cchengoran525/HappyMac/training/analysis/02_x_distribution.png

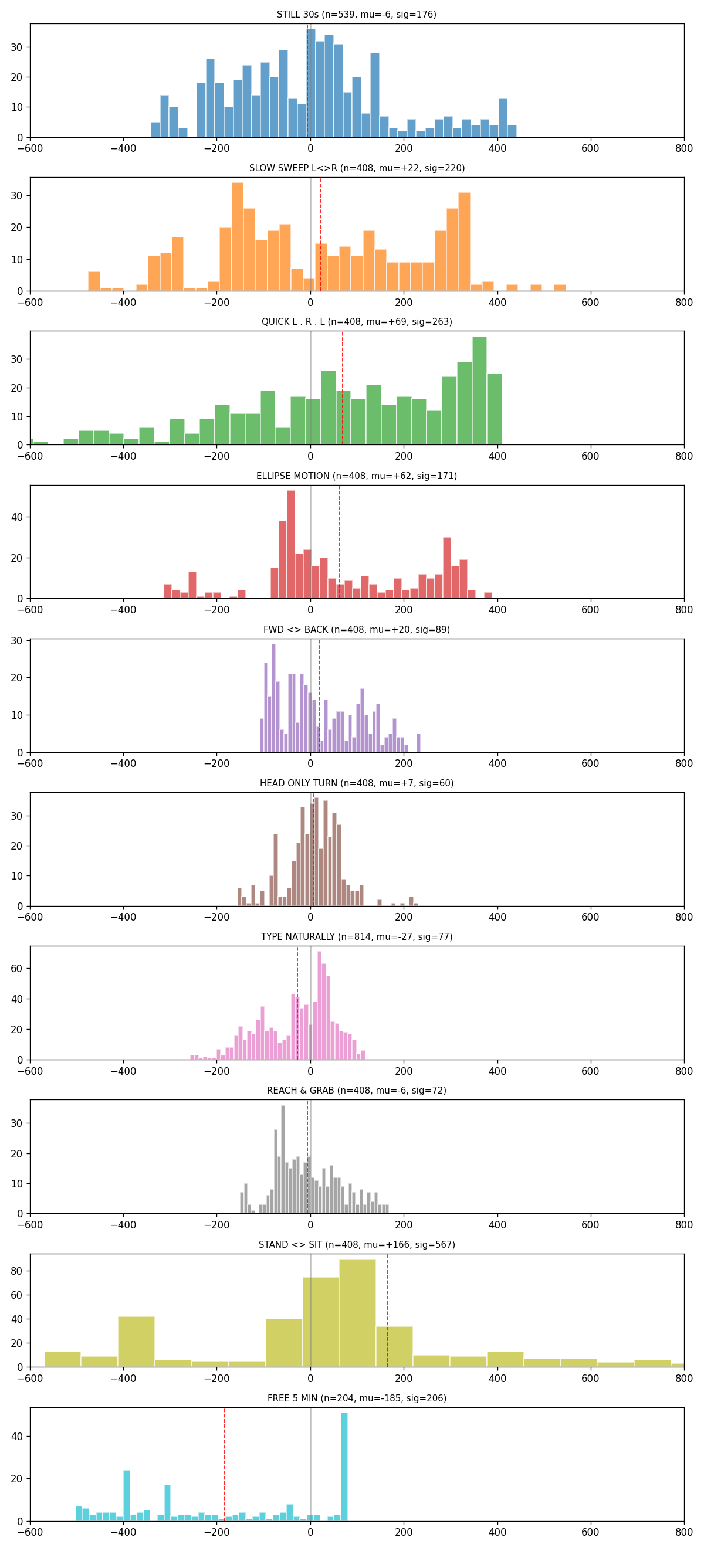
training/analysis/02_x_distribution.png
