cchengoran525/HappyMac/training/analysis/04_drift_analysis.png

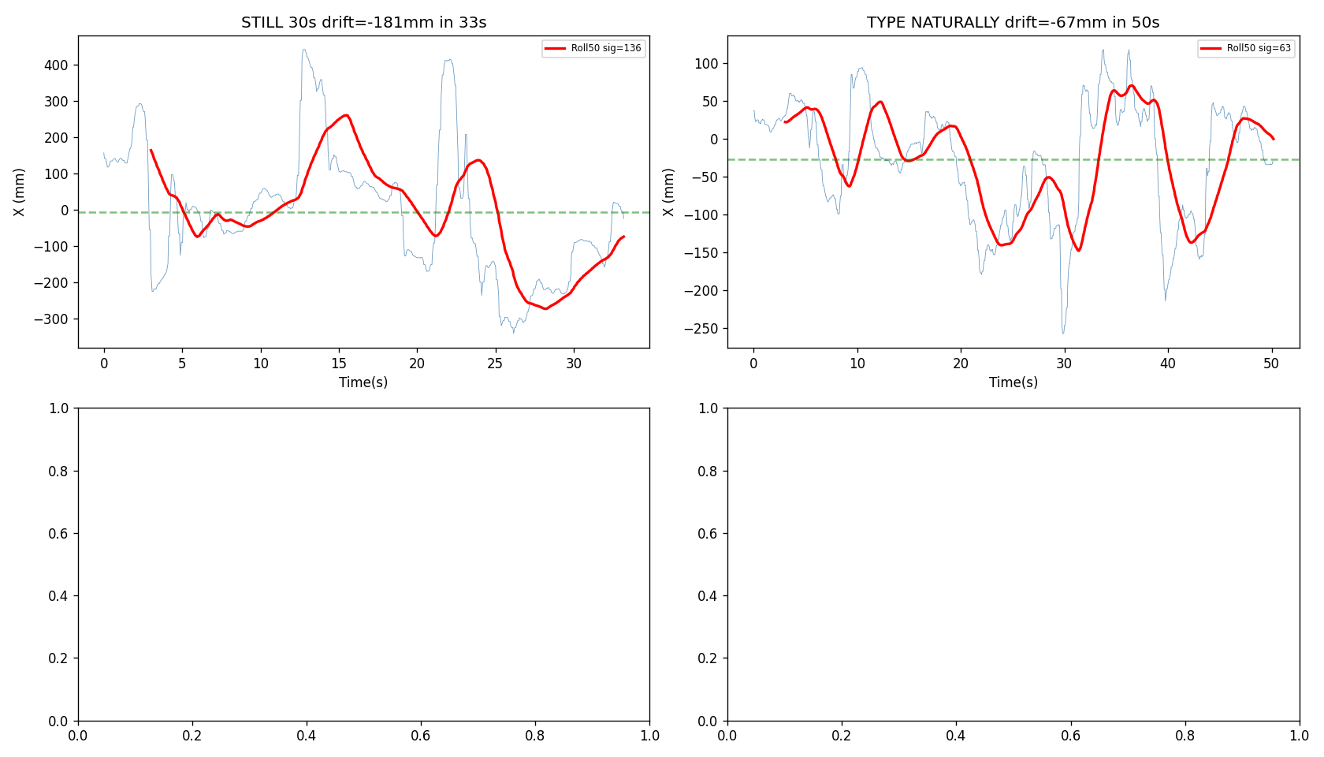
training/analysis/04_drift_analysis.png
