cchengoran525/HappyMac/training/analysis/05_x_vs_ld2410c.png

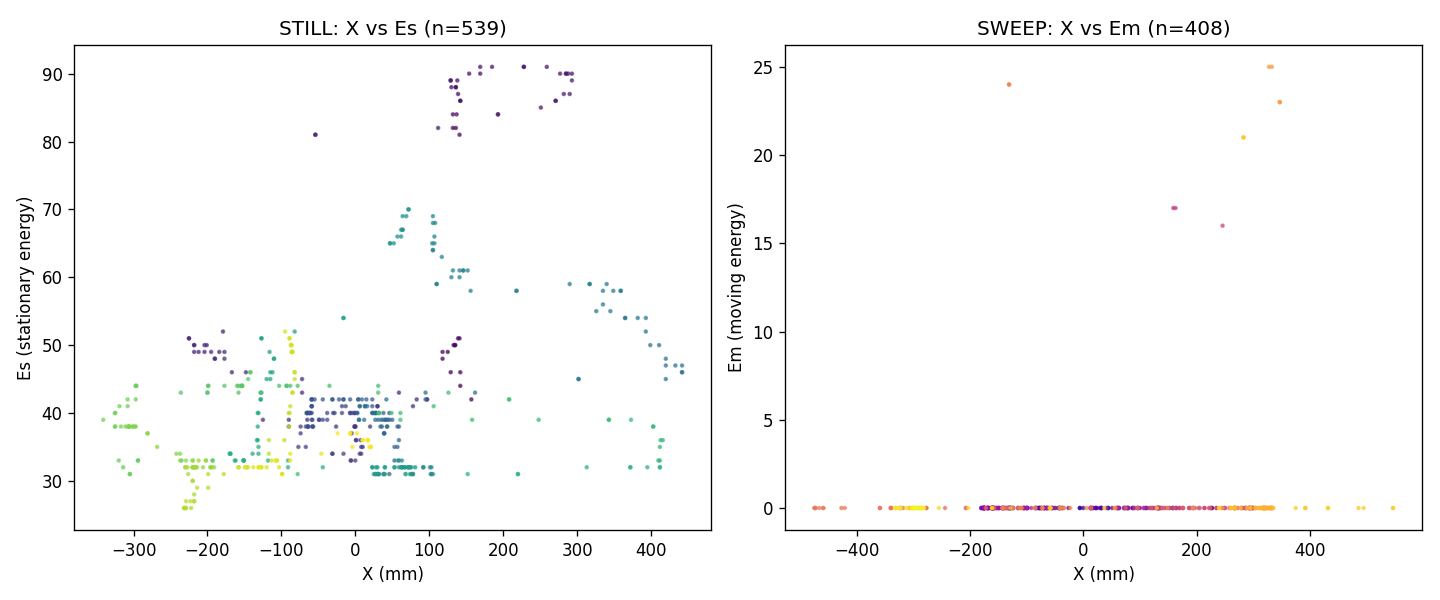
training/analysis/05_x_vs_ld2410c.png
