cchengoran525/HappyMac/training/analysis/06_research_panel.png

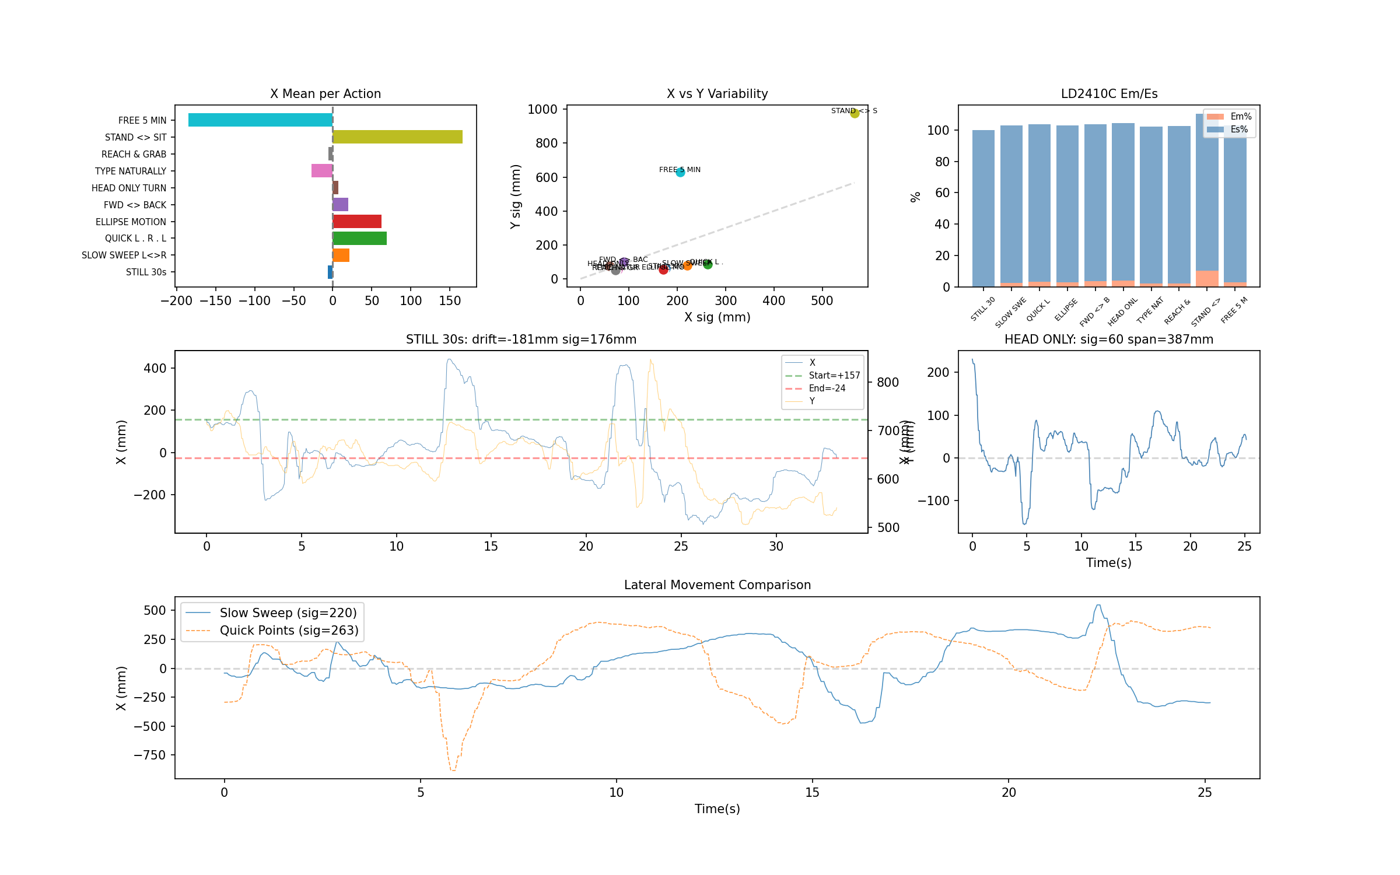
training/analysis/06_research_panel.png
