cchengoran525/HappyMac/training/analysis/07_vision_vs_radar.png

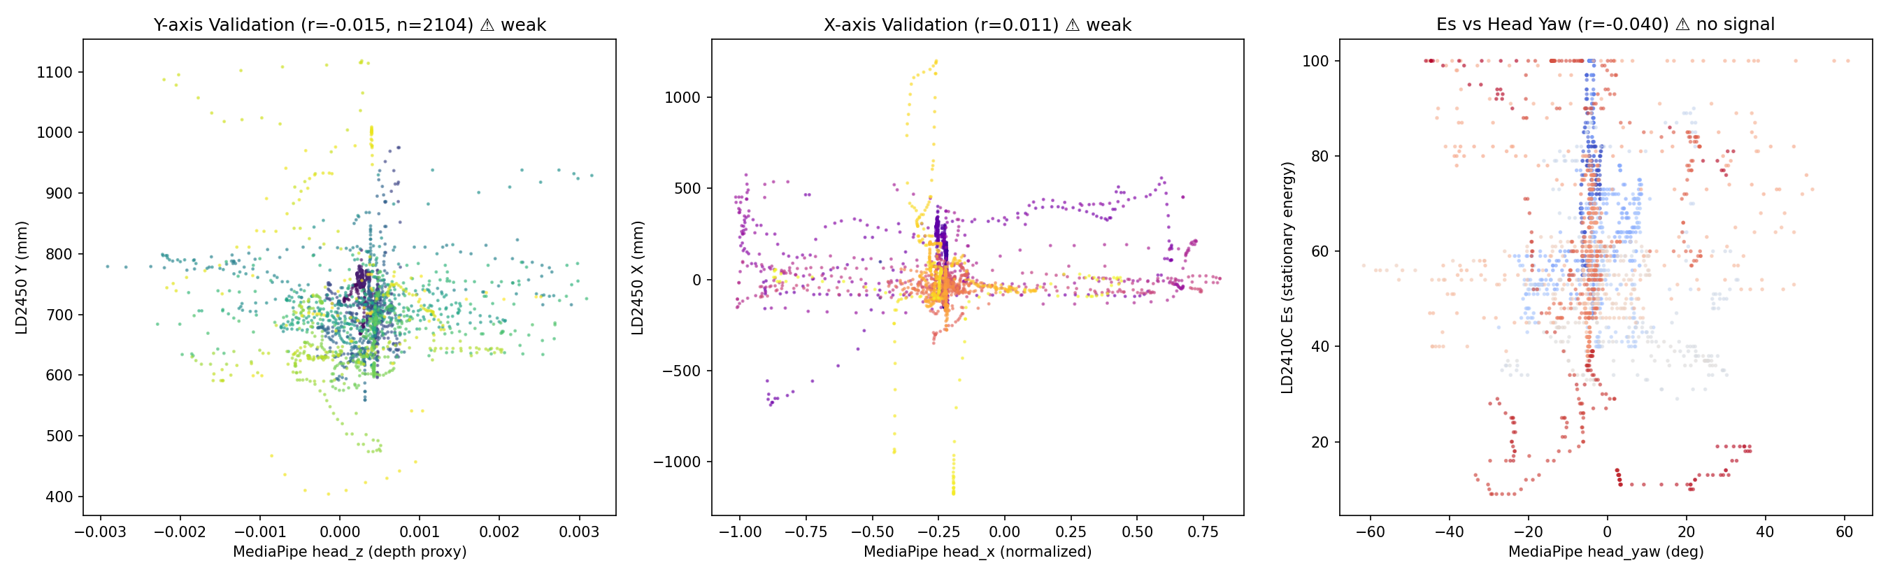
training/analysis/07_vision_vs_radar.png
