cchengoran525/HappyMac/training/analysis/07_vision_vs_radar_20260813_165801.png

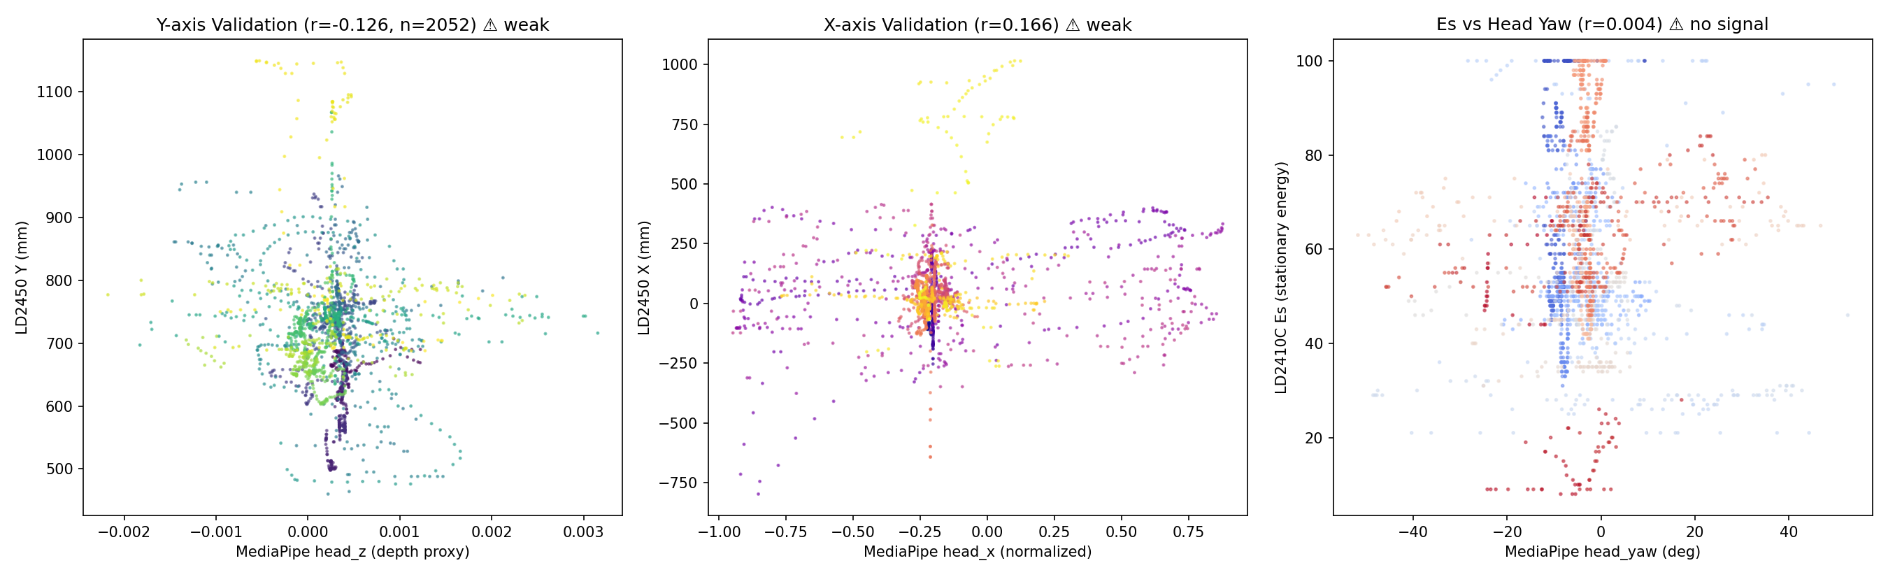
training/analysis/07_vision_vs_radar_20260813_165801.png
