cchengoran525/HappyMac/training/analysis/07_vision_vs_radar_20260813_170609.png

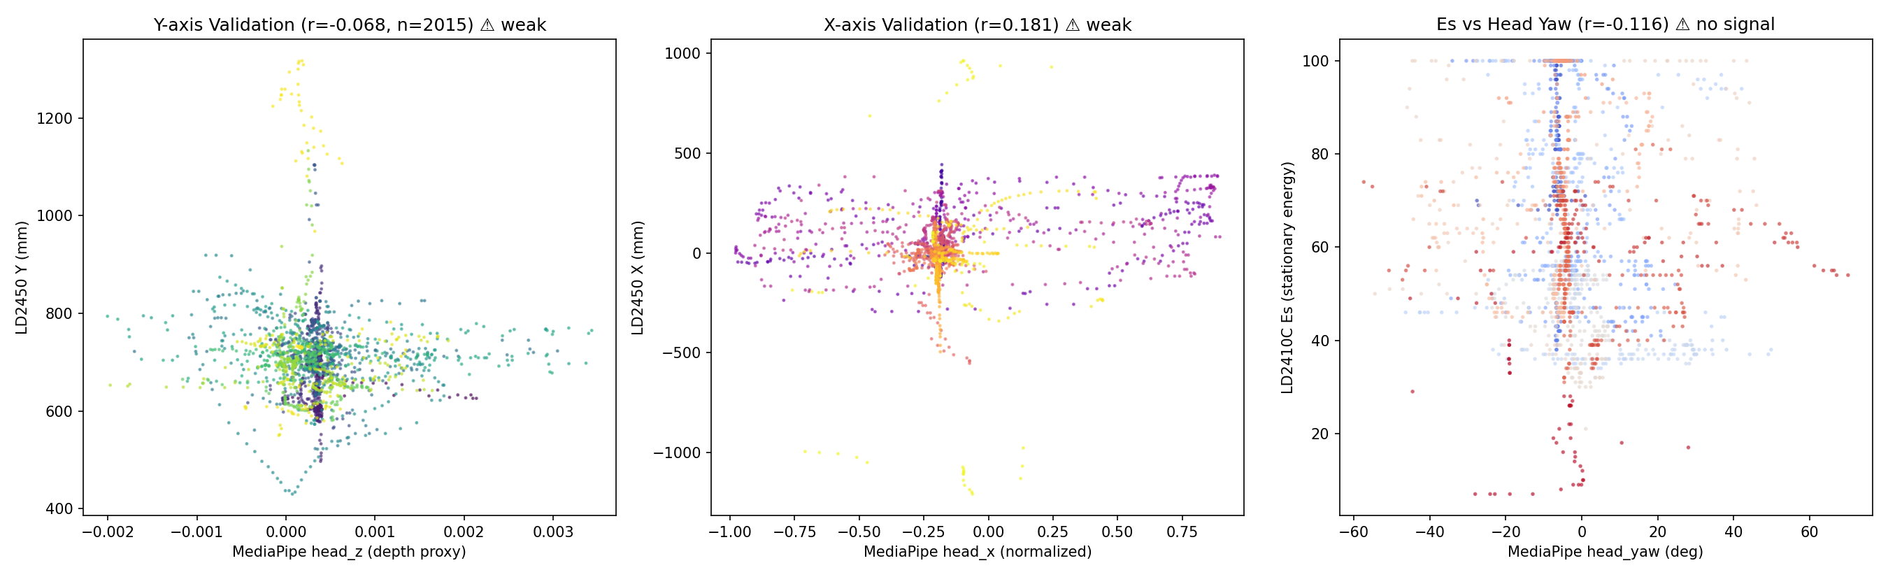
training/analysis/07_vision_vs_radar_20260813_170609.png
