cchengoran525/HappyMac/training/analysis/08_camera_vs_radar_timeseries.png

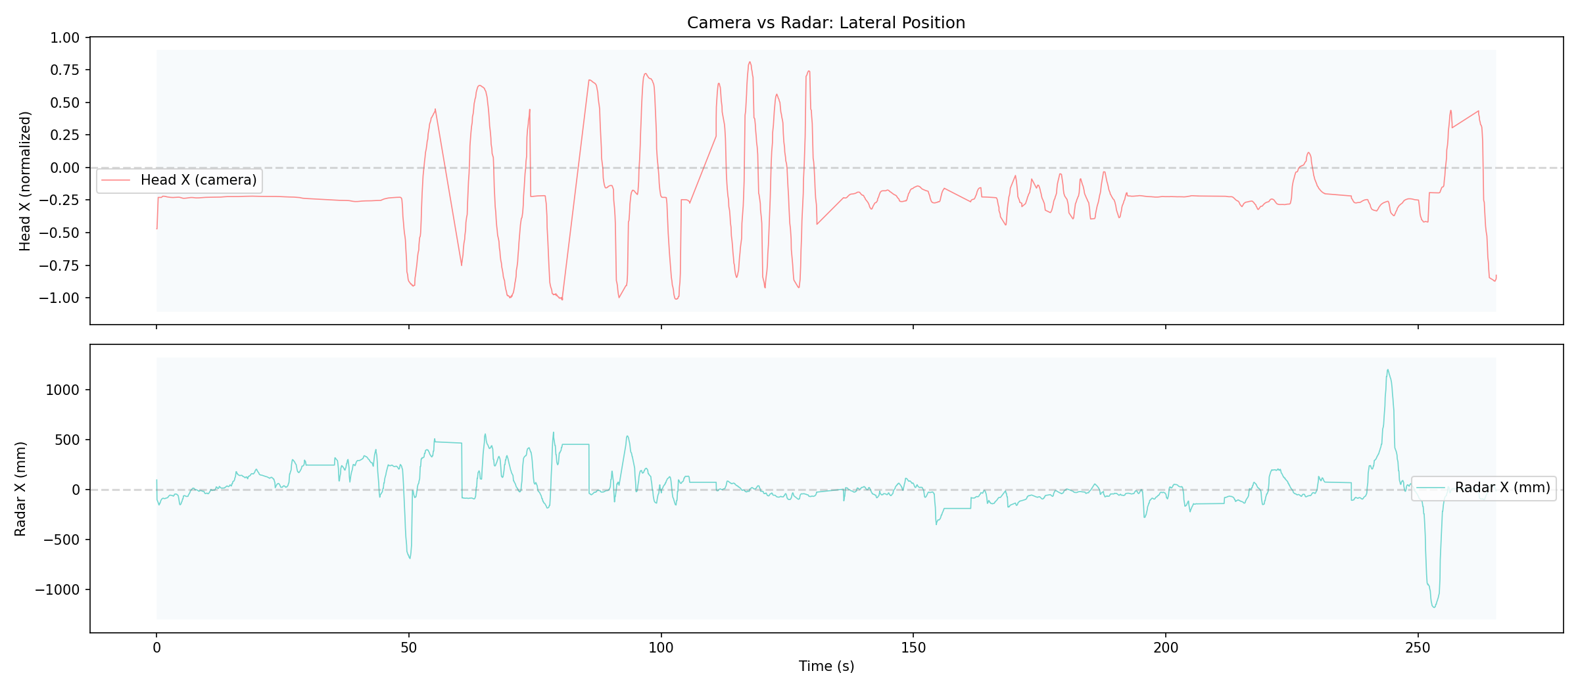
training/analysis/08_camera_vs_radar_timeseries.png
