cchengoran525/HappyMac/training/analysis/08_camera_vs_radar_timeseries_20260813_170609.png

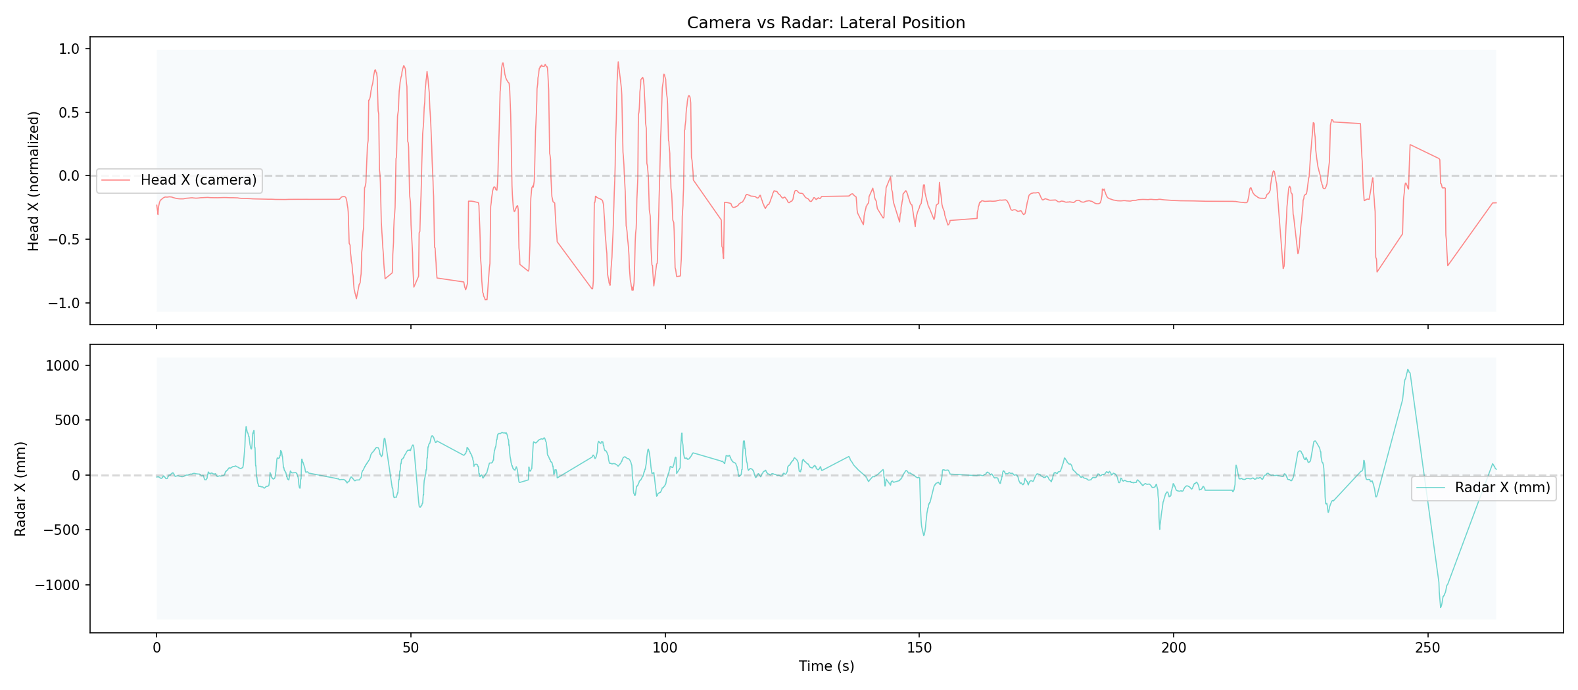
training/analysis/08_camera_vs_radar_timeseries_20260813_170609.png
