cchengoran525/HappyMac/training/analysis/09_yaw_vs_es_20260813_160414.png

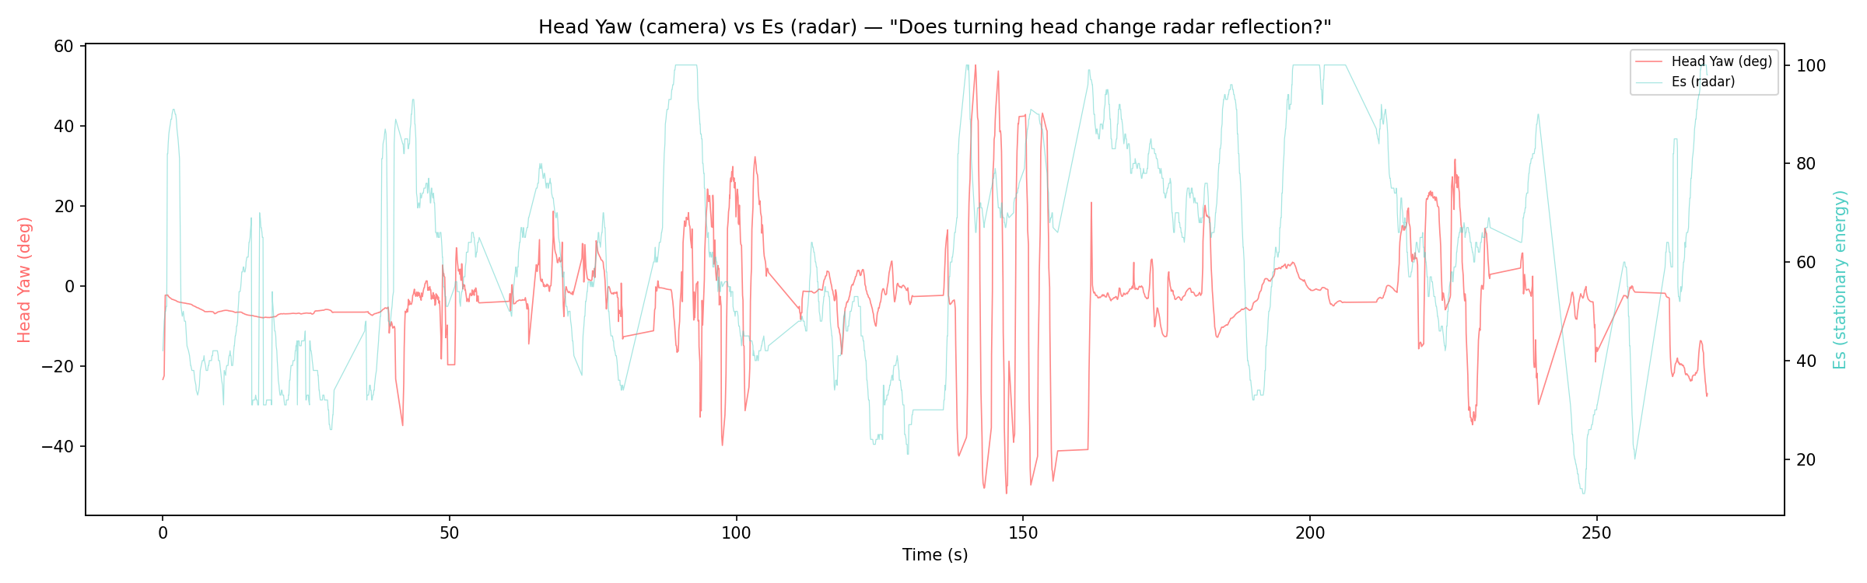
training/analysis/09_yaw_vs_es_20260813_160414.png
