cchengoran525/HappyMac/training/analysis/09_yaw_vs_es_20260813_170609.png

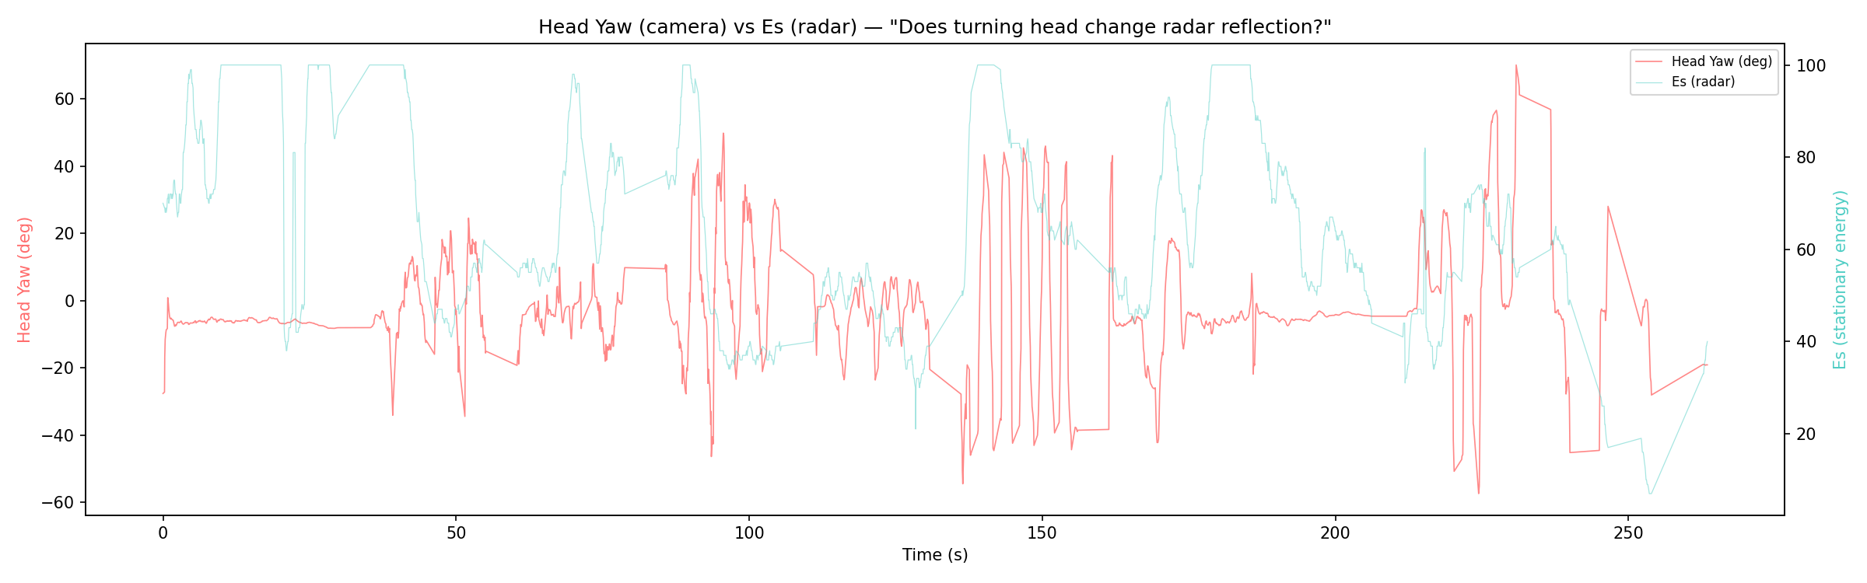
training/analysis/09_yaw_vs_es_20260813_170609.png
