cchengoran525/HappyMac/new_radar/new_radar.ino

// ============================================================
//  HappyMac — new_radar.ino (TinyML 数据采集版 — V2 collection)
//
//  功能：双雷达同时采样 + 串口 CSV 输出
//    - LD2450: X/Y 坐标 + 速度（10Hz，3 目标全量）
//    - LD2410C: 移动/静止能量 + 距离 + 存在标志
//    - SR602: 红外二值信号
//
//  输出格式（115200 baud, USB CDC）：
//    RADAR,<ms>,<x>,<y>,<v>,<x2>,<y2>,<v2>,<x3>,<y3>,<v3>,<em>,<es>,<d2410>,<pres>,<ir>
//      ms        = 毫秒时间戳
//      x,y,v     = LD2450 目标 1 坐标(mm) + 速度(cm/s)
//      x2,y2,v2  = LD2450 目标 2（无目标时为 0）
//      x3,y3,v3  = LD2450 目标 3（无目标时为 0）
//      em,es     = LD2410C moving/stationary energy
//      d2410     = LD2410C 距离(cm)
//      pres      = LD2410C presence (1/0)
//      ir        = SR602 (1/0)
//
//  V2 变更（DATA_COLLECTION_V2.md）：
//    1. FW_VERSION 宏 — 启动打印 + CSV 首行
//    2. LD2410C 灵敏度 40/40（V1 为 80/80，宏可切换做 AB 实验）
//    3. 3 目标全量 CSV（V1 只取第 1 目标）
//
//  硬件：ESP32-C3 SuperMini + SH1106 OLED + LD2450 + LD2410C + SR602
//  烧录：CDCOnBoot=cdc（必须！v3 core 默认 USB CDC 关闭）
// ============================================================

// ─── 版本 & 可配宏 ────────────────────────────────────
#define FW_VERSION "collection_v2.0"

// LD2410C gate 0-3 灵敏度阈值（V1=80, V2=40; 改回 80 做 AB 对照）
#ifndef LD2410_SENSITIVITY
#define LD2410_SENSITIVITY 40
#endif

#include <Arduino.h>
#include <Wire.h>
#include <U8g2lib.h>
#include <ld2410.h>
#include <HardwareSerial.h>

// ─── 引脚 ──────────────────────────────────────────
#define PIN_SDA       8
#define PIN_SCL       9
#define PIN_IR        5       // SR602
#define PIN_2410_RX   4
#define PIN_2410_TX   3
#define PIN_2450_RX   20
#define PIN_2450_TX   21
#define RADAR_BAUD    256000

// ─── EMA 滤波 ──────────────────────────────────────
#define EMA_A 0.55f
float   flt_x=0, flt_y=0;
bool    flt_ok=false;

// ─── 硬件 ──────────────────────────────────────────
U8G2_SH1106_128X64_NONAME_F_HW_I2C oled(U8G2_R0, U8X8_PIN_NONE);
ld2410 radar2410;
HardwareSerial radar2450(0);

// ─── LD2450 ─────────────────────────────────────────
int16_t  r50_x=0, r50_y=0, r50_v=0;    // 目标 1
int16_t  r50_x2=0, r50_y2=0, r50_v2=0; // 目标 2
int16_t  r50_x3=0, r50_y3=0, r50_v3=0; // 目标 3
bool     r50_ok=false;
uint32_t r50_last=0;

// ─── LD2410C ────────────────────────────────────────
int  r10_em=0, r10_es=0, r10_dist=0;
bool r10_pres=false;

// ─── LD2450 帧解析（V2: 3 目标全量）──────────────────
uint8_t b[64]; int bi=0;
void parse2450(){
  while(radar2450.available()){
    b[bi++]=radar2450.read();
    if(bi>=30){
      if(b[0]==0xAA&&b[1]==0xFF&&b[2]==0x03&&b[3]==0x00&&b[28]==0x55&&b[29]==0xCC){
        // 清零所有目标
        r50_x=0; r50_y=0; r50_v=0;
        r50_x2=0; r50_y2=0; r50_v2=0;
        r50_x3=0; r50_y3=0; r50_v3=0;
        r50_ok=false;

        int16_t* targets_x[] = {&r50_x, &r50_x2, &r50_x3};
        int16_t* targets_y[] = {&r50_y, &r50_y2, &r50_y3};
        int16_t* targets_v[] = {&r50_v, &r50_v2, &r50_v3};

        for(int t=0;t<3;t++){
          int o=4+t*8;
          int16_t rx=b[o]|b[o+1]<<8, ry=b[o+2]|b[o+3]<<8, rv=b[o+4]|b[o+5]<<8;
          int x=(rx&0x8000)?(rx&0x7FFF):-(rx&0x7FFF);
          int y=(ry&0x8000)?(ry&0x7FFF):-(ry&0x7FFF);
          int v=(rv&0x8000)?(rv&0x7FFF):-(rv&0x7FFF);
          *targets_x[t] = x;
          *targets_y[t] = y;
          *targets_v[t] = v;
          if(!(x==0&&y==0)) r50_ok=true;
        }

        // EMA 滤波（仅对主目标）
        if(r50_ok && !(r50_x==0&&r50_y==0)){
          if(!flt_ok){flt_x=r50_x; flt_y=r50_y; flt_ok=true;}
          else{
            flt_x=EMA_A*r50_x+(1.0f-EMA_A)*flt_x;
            flt_y=EMA_A*r50_y+(1.0f-EMA_A)*flt_y;
          }
        }

        r50_last=millis(); bi=0;
      }else{memmove(b,b+1,--bi);}
    }
  }
}

// ─── 串口命令（电脑 → C3 OLED 显示）─────────────────
char  cmd_phase[32] = "";
int   cmd_countdown  = 0;
int   cmd_state      = 0;  // 0=无, 1=倒计时, 2=开始, 3=完成
uint32_t cmd_expiry  = 0;

void checkCmd() {
  while (Serial.available()) {
    String s = Serial.readStringUntil('\n');
    s.trim();
    if (!s.startsWith("!")) continue;
    s = s.substring(1);
    if (s.startsWith("PHASE:")) {
      // !PHASE:静止基线,3
      int comma = s.indexOf(',');
      if (comma > 0) {
        String name = s.substring(6, comma);
        name.toCharArray(cmd_phase, sizeof(cmd_phase));
        cmd_countdown = s.substring(comma + 1).toInt();
        cmd_state = 1;
        cmd_expiry = millis() + 5000;
      }
    } else if (s == "GO") {
      cmd_state = 2; cmd_expiry = millis() + 3000;
    } else if (s == "DONE") {
      cmd_state = 3; cmd_expiry = millis() + 2000;
    } else if (s == "CLEAR") {
      cmd_state = 0; cmd_phase[0] = 0;
    } else if (s == "SYNC") {
      Serial.printf("!SYNC,%lu\n", millis());  // 回复时间戳给电脑
    } else if (s == "START") {
      // 记录正式录制起点；上位机同时保存自己的墙钟时间。
      Serial.printf("!START,%lu\n", millis());
    }
  }
  if (cmd_state && millis() > cmd_expiry) {
    cmd_state = 0;
  }
}
void setup(){
  Serial.begin(115200);
  pinMode(PIN_IR,INPUT);
  Wire.begin(PIN_SDA,PIN_SCL);
  oled.begin(); oled.setContrast(200);
  oled.clearBuffer(); oled.setFont(u8g2_font_6x10_tr);
  oled.drawStr(15,20,"HappyMac"); oled.drawStr(0,36,"2-radar collect");
  oled.sendBuffer();

  // LD2410C — 配置灵敏度（V2: 40/40 恢复 Em 通道）
  Serial1.begin(RADAR_BAUD,SERIAL_8N1,PIN_2410_RX,PIN_2410_TX);
  {unsigned long t=millis()+2000; while(millis()<t) while(Serial1.available())Serial1.read();}
  if(radar2410.begin(Serial1)){
    Serial.println("[2410] OK");
    delay(100);
    for(int g=0;g<4;g++) radar2410.setGateSensitivityThreshold(g,LD2410_SENSITIVITY,LD2410_SENSITIVITY);
    Serial.printf("[2410] sensitivity: gates 0-3 = %d/%d\n", LD2410_SENSITIVITY, LD2410_SENSITIVITY);
  }else{Serial.println("[2410] WARN");}

  // LD2450
  radar2450.begin(RADAR_BAUD,SERIAL_8N1,PIN_2450_RX,PIN_2450_TX);
  {unsigned long t=millis()+2000; while(millis()<t) while(radar2450.available())radar2450.read();}
  Serial.println("[2450] OK");

  // SYNC 标记（摄像头对齐用，采集脚本检测此标记）
  for(int i=0;i<10;i++){
    Serial.printf("!SYNC,%lu\n",millis());
    delay(50);
  }

  Serial.printf("!FW_VERSION,%s\n", FW_VERSION);
  Serial.println("CSV: ms,x,y,v,x2,y2,v2,x3,y3,v3,em,es,d2410,pres,ir");
}

// ─── loop ───────────────────────────────────────────
void loop(){
  // ── 读电脑发来的 OLED 命令 ──
  checkCmd();

  // ── 读 LD2410C（始终读双通道能量，不依赖检测标志）──
  radar2410.read();
  r10_pres=radar2410.movingTargetDetected()||radar2410.stationaryTargetDetected();
  r10_em=radar2410.movingTargetEnergy();
  r10_es=radar2410.stationaryTargetEnergy();
  if(radar2410.movingTargetDetected()) r10_dist=radar2410.movingTargetDistance();
  else if(radar2410.stationaryTargetDetected()) r10_dist=radar2410.stationaryTargetDistance();
  else r10_dist=0;

  // ── 读 LD2450 ──
  parse2450();
  if(r50_ok&&(millis()-r50_last)>500)r50_ok=false;

  // ── IR ──
  bool ir=(digitalRead(PIN_IR)==HIGH);

  // ── OLED（5Hz, 200ms）────────────────────────────
  static uint32_t ot=0;
  if(millis()-ot>=80){   // OLED 刷新 ~12Hz, 延迟 80ms
    ot=millis();
    oled.clearBuffer();
    char line[32];

    if(r50_ok){
      // 小字 raw 诊断
      oled.setFont(u8g2_font_5x8_tr);
      snprintf(line,sizeof(line),"raw X:%+4d Y:%4d V:%+3d", r50_x,r50_y,r50_v);
      oled.drawStr(0, 6, line);
      snprintf(line,sizeof(line),"Em:%3d Es:%3d D:%3d %s IR:%c",
        r10_em,r10_es,r10_dist, r10_pres?"P":"-", ir?'Y':'N');
      oled.drawStr(0, 13, line);

      // 大字 EMA
      oled.setFont(u8g2_font_7x13B_tr);
      snprintf(line,sizeof(line),"X%+4d",-(int)flt_x); oled.drawStr(0,30,line);  // OLED镜像
      snprintf(line,sizeof(line),"Y%4d",(int)flt_y);  oled.drawStr(64,30,line);

      // 速度
      oled.setFont(u8g2_font_5x8_tr);
      int dx=r50_x-(int)flt_x, dy=r50_y-(int)flt_y;
      snprintf(line,sizeof(line),"V%+4d %s", r50_v,
        (abs(dx)>80||abs(dy)>60||abs(r50_v)>10)?"MOVING":"steady");
      oled.drawStr(0,40,line);

      // 阶段覆盖（电脑发指令）或俯视图
      if(cmd_state!=0){
        oled.setFont(u8g2_font_6x10_tr); oled.drawStr(0,50,cmd_phase);
        if(cmd_state==1){
          snprintf(line,sizeof(line),"%d",cmd_countdown);
          oled.setFont(u8g2_font_10x20_tn);
          oled.drawStr(64-strlen(line)*5,53,line);
        }else if(cmd_state==2){
          oled.setFont(u8g2_font_7x13B_tr); oled.drawStr(10,58,">>> GO <<<");
        }else if(cmd_state==3){
          oled.setFont(u8g2_font_7x13B_tr); oled.drawStr(20,58,"DONE");
        }
      }else{
        oled.drawHLine(0,53,128); oled.drawVLine(63,42,20); oled.drawDisc(63,62,2);
        int lx=map(-200,-800,800,0,127), rx=map(200,-800,800,0,127);
        oled.drawVLine(lx,56,6); oled.drawVLine(rx,56,6);
        int prx=map(constrain(-r50_x,-800,800),-800,800,0,127);  // OLED镜像
        int pry=map(constrain(r50_y,0,2000),0,2000,63,44);
        oled.drawPixel(prx-1,pry); oled.drawPixel(prx+1,pry);
        oled.drawPixel(prx,pry-1); oled.drawPixel(prx,pry+1);
        int pex=map(constrain(-(int)flt_x,-800,800),-800,800,0,127);  // OLED镜像
        int pey=map(constrain((int)flt_y,0,2000),0,2000,63,44);
        oled.drawDisc(pex,pey,2);
      }
    }else{
      oled.setFont(u8g2_font_7x13B_tr); oled.drawStr(15,28,"no target");
    }
    oled.sendBuffer();
  }

  // ── 串口输出（非阻塞，缓冲区不足时自动跳过）──
  static uint8_t serial_skip=0;
  if(Serial && ++serial_skip>=2){  // 每 2 帧发一次，降低缓冲压力
    serial_skip=0;
    if(Serial.availableForWrite()>80){  // 确保有空间，避免阻塞
      Serial.printf("RADAR,%lu,%d,%d,%d,%d,%d,%d,%d,%d,%d,%d,%d,%d,%d,%d\n",
        millis(),
        r50_ok?r50_x:0, r50_ok?r50_y:0, r50_ok?r50_v:0,
        r50_ok?r50_x2:0, r50_ok?r50_y2:0, r50_ok?r50_v2:0,
        r50_ok?r50_x3:0, r50_ok?r50_y3:0, r50_ok?r50_v3:0,
        r10_em, r10_es, r10_dist,
        r10_pres?1:0, ir?1:0);
    }
  }
  delay(20);  // 30→20ms, 主循环 ~30Hz
}
